sidjain24680-lgtm/Universal-Retro-fit-Assistive-Smart-Suitcase-Attachment/Images/Back View.png

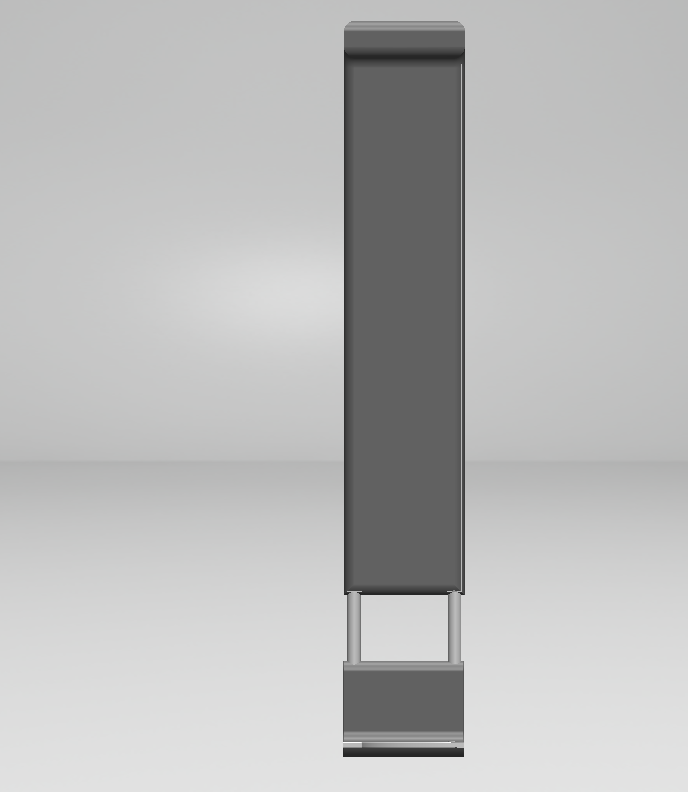
Images/Back View.png
