sidjain24680-lgtm/Universal-Retro-fit-Assistive-Smart-Suitcase-Attachment/Images/Base Front.png

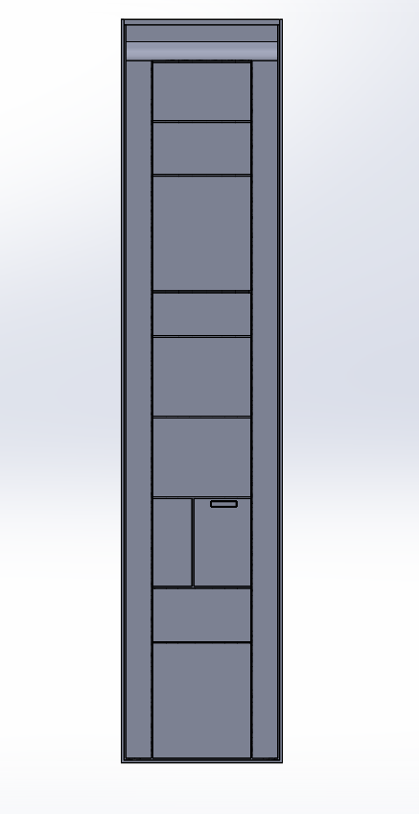
Images/Base Front.png
