sidjain24680-lgtm/Universal-Retro-fit-Assistive-Smart-Suitcase-Attachment/Images/Base isometric.png

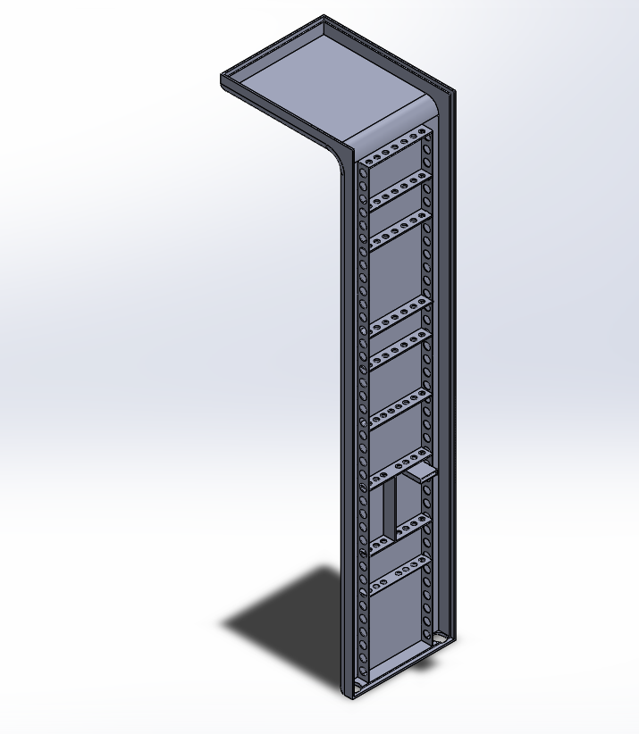
Images/Base isometric.png
