sidjain24680-lgtm/Universal-Retro-fit-Assistive-Smart-Suitcase-Attachment/Images/Bottom.png

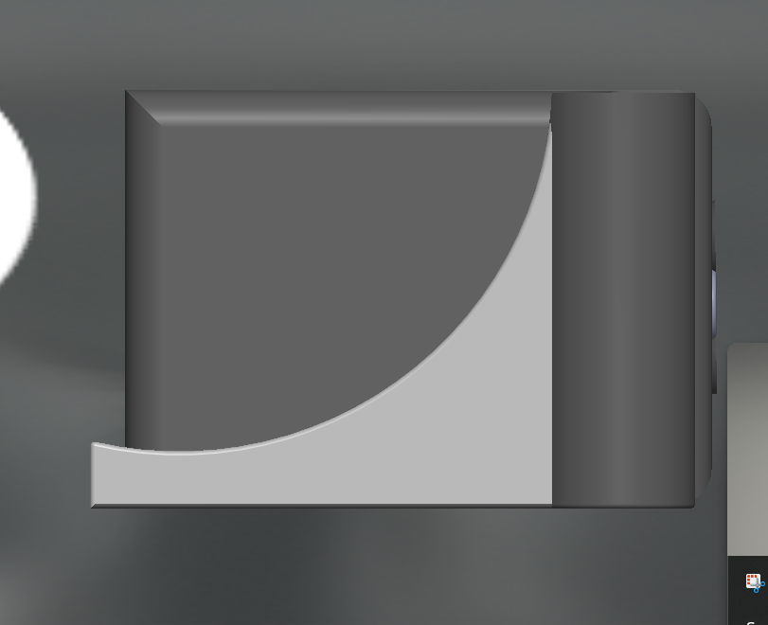
Images/Bottom.png
