sidjain24680-lgtm/Universal-Retro-fit-Assistive-Smart-Suitcase-Attachment/Images/Exploaded View.png

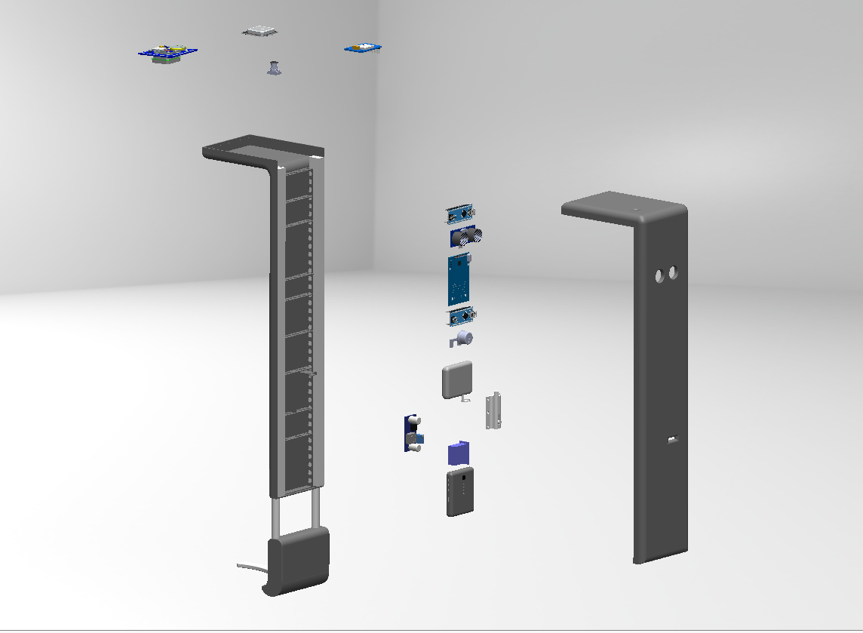
Images/Exploaded View.png
