sidjain24680-lgtm/Universal-Retro-fit-Assistive-Smart-Suitcase-Attachment/Images/Screenshot 2026-01-17 222351 - Copy.png

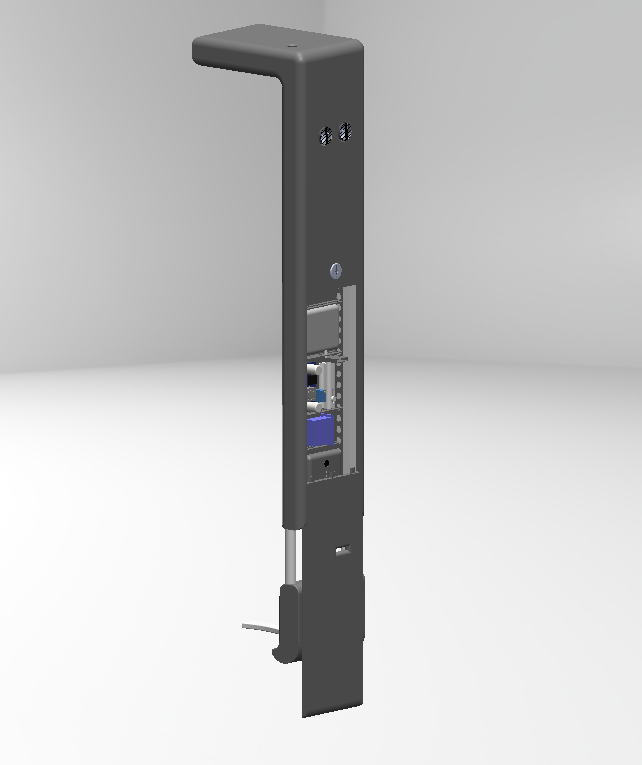
Images/Screenshot 2026-01-17 222351 - Copy.png
