sidjain24680-lgtm/Universal-Retro-fit-Assistive-Smart-Suitcase-Attachment/Images/Sliding gate mechanism.png

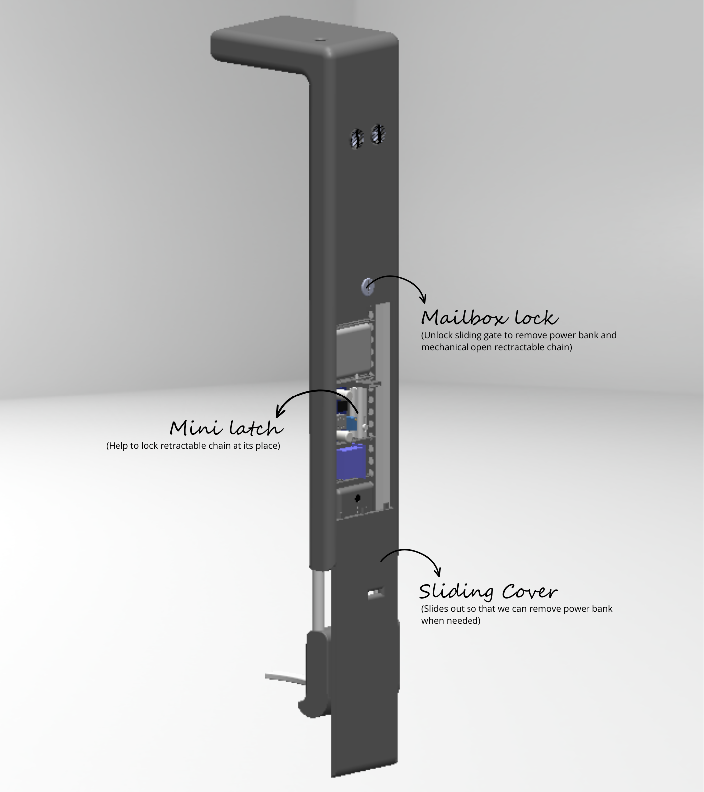
Images/Sliding gate mechanism.png
